openLRSng/openLRSng/openLRSng/RFM.h

#ifndef _RFM_H
#define _RFM_H

// register addresses
#define RFM22B_INTSTAT1     0x03
#define RFM22B_INTSTAT2     0x04
#define RFM22B_INTEN1        0x05
#define RFM22B_INTEN2        0x06
#define RFM22B_OPMODE1     0x07
#define RFM22B_OPMODE2     0x08
#define RFM22B_XTALCAP      0x09
#define RFM22B_MCUCLK       0x0A
#define RFM22B_GPIOCFG0    0x0B
#define RFM22B_GPIOCFG1    0x0C
#define RFM22B_GPIOCFG2    0x0D
#define RFM22B_IOPRTCFG    0x0E

#define RFM22B_IFBW           0x1C
#define RFM22B_AFCLPGR      0x1D
#define RFM22B_AFCTIMG      0x1E
#define RFM22B_RXOSR         0x20
#define RFM22B_NCOFF2       0x21
#define RFM22B_NCOFF1       0x22
#define RFM22B_NCOFF0       0x23
#define RFM22B_CRGAIN1     0x24
#define RFM22B_CRGAIN0     0x25
#define RFM22B_RSSI           0x26
#define RFM22B_AFCLIM       0x2A
#define RFM22B_AFC0          0x2B
#define RFM22B_AFC1          0x2C

#define RFM22B_DACTL    0x30
#define RFM22B_HDRCTL1    0x32
#define RFM22B_HDRCTL2    0x33
#define RFM22B_PREAMLEN  0x34
#define RFM22B_PREATH      0x35
#define RFM22B_SYNC3        0x36
#define RFM22B_SYNC2        0x37
#define RFM22B_SYNC1        0x38
#define RFM22B_SYNC0        0x39

#define RFM22B_TXHDR3      0x3A
#define RFM22B_TXHDR2      0x3B
#define RFM22B_TXHDR1      0x3C
#define RFM22B_TXHDR0      0x3D
#define RFM22B_PKTLEN       0x3E
#define RFM22B_CHKHDR3    0x3F
#define RFM22B_CHKHDR2   0x40
#define RFM22B_CHKHDR1   0x41
#define RFM22B_CHKHDR0   0x42
#define RFM22B_HDREN3     0x43
#define RFM22B_HDREN2     0x44
#define RFM22B_HDREN1     0x45
#define RFM22B_HDREN0     0x46
#define RFM22B_RXPLEN      0x4B

#define RFM22B_TXPOWER   0x6D
#define RFM22B_TXDR1        0x6E
#define RFM22B_TXDR0        0x6F

#define RFM22B_MODCTL1      0x70
#define RFM22B_MODCTL2      0x71
#define RFM22B_FREQDEV      0x72
#define RFM22B_FREQOFF1     0x73
#define RFM22B_FREQOFF2     0x74
#define RFM22B_BANDSEL      0x75
#define RFM22B_CARRFREQ1  0x76
#define RFM22B_CARRFREQ0  0x77
#define RFM22B_FHCH           0x79
#define RFM22B_FHS             0x7A
#define RFM22B_TX_FIFO_CTL1    0x7C
#define RFM22B_TX_FIFO_CTL2    0x7D
#define RFM22B_RX_FIFO_CTL     0x7E
#define RFM22B_FIFO            0x7F

// register fields
#define RFM22B_OPMODE_POWERDOWN    0x00
#define RFM22B_OPMODE_READY    0x01  // enable READY mode
#define RFM22B_OPMODE_TUNE      0x02  // enable TUNE mode
#define RFM22B_OPMODE_RX      0x04  // enable RX mode
#define RFM22B_OPMODE_TX      0x08  // enable TX mode
#define RFM22B_OPMODE_32K      0x10  // enable internal 32k xtal
#define RFM22B_OPMODE_WUT    0x40  // wake up timer
#define RFM22B_OPMODE_LBD     0x80  // low battery detector

#define RFM22B_PACKET_SENT_INTERRUPT               0x04
#define RFM22B_RX_PACKET_RECEIVED_INTERRUPT   0x02

void rfmInit(uint8_t diversity);
void rfmClearInterrupts(void);
void rfmClearIntStatus(void);
void rfmClearFIFO(uint8_t diversity);
void rfmSendPacket(uint8_t* pkt, uint8_t size);

uint16_t rfmGetAFCC(void);
uint8_t rfmGetGPIO1(void);
uint8_t rfmGetRSSI(void);
uint8_t rfmGetPacketLength(void);
void rfmGetPacket(uint8_t *buf, uint8_t size);

void rfmSetTX(void);
void rfmSetRX(void);
void rfmSetCarrierFrequency(uint32_t f);
void rfmSetChannel(uint8_t ch);
void rfmSetDirectOut(uint8_t enable);
void rfmSetHeader(uint8_t iHdr, uint8_t bHdr);
void rfmSetModemRegs(struct rfm22_modem_regs* r);
void rfmSetPower(uint8_t p);
void rfmSetReadyMode(void);
void rfmSetStepSize(uint8_t sp);

void rfmInit(uint8_t diversity)
{
  spiWriteRegister(RFM22B_INTEN2, 0x00);    // disable interrupts
  spiWriteRegister(RFM22B_INTEN1, 0x00);    // disable interrupts
  spiWriteRegister(RFM22B_XTALCAP, 0x7F);   // XTAL cap = 12.5pF
  spiWriteRegister(RFM22B_MCUCLK, 0x05);    // 2MHz clock

  spiWriteRegister(RFM22B_GPIOCFG2, (diversity ? 0x17 : 0xFD) ); // gpio 2 ant. sw, 1 if diversity on else VDD
  spiWriteRegister(RFM22B_PREAMLEN, (diversity ? 0x14 : 0x0A) );    // 40 bit preamble, 80 with diversity
  spiWriteRegister(RFM22B_IOPRTCFG, 0x00);    // gpio 0,1,2 NO OTHER FUNCTION.

  #ifdef SWAP_GPIOS
  spiWriteRegister(RFM22B_GPIOCFG0, 0x15);    // gpio0 RX State
  spiWriteRegister(RFM22B_GPIOCFG1, 0x12);    // gpio1 TX State
  #else
  spiWriteRegister(RFM22B_GPIOCFG0, 0x12);    // gpio0 TX State
  spiWriteRegister(RFM22B_GPIOCFG1, 0x15);    // gpio1 RX State
  #endif

  // Packet settings
  spiWriteRegister(RFM22B_DACTL, 0x8C);    // enable packet handler, msb first, enable crc,
  spiWriteRegister(RFM22B_HDRCTL1, 0x0F);    // no broadcast, check header bytes 3,2,1,0
  spiWriteRegister(RFM22B_HDRCTL2, 0x42);    // 4 byte header, 2 byte sync, variable packet size
  spiWriteRegister(RFM22B_PREATH, 0x2A);    // preamble detect = 5 (20bits), rssioff = 2
  spiWriteRegister(RFM22B_SYNC3, 0x2D);    // sync word 3
  spiWriteRegister(RFM22B_SYNC2, 0xD4);    // sync word 2
  spiWriteRegister(RFM22B_SYNC1, 0x00);    // sync word 1 (not used)
  spiWriteRegister(RFM22B_SYNC0, 0x00);    // sync word 0 (not used)
  spiWriteRegister(RFM22B_HDREN3, 0xFF);    // must set all bits
  spiWriteRegister(RFM22B_HDREN2, 0xFF);    // must set all bits
  spiWriteRegister(RFM22B_HDREN1, 0xFF);    // must set all bits
  spiWriteRegister(RFM22B_HDREN0, 0xFF);    // must set all bits

  spiWriteRegister(RFM22B_FREQOFF1, 0x00);    // no offset
  spiWriteRegister(RFM22B_FREQOFF2, 0x00);    // no offset
  spiWriteRegister(RFM22B_FHCH,        0x00);   // set to hop channel 0
}

void rfmClearFIFO(uint8_t diversity)
{
  //clear FIFO, disable multi-packet, enable diversity if needed
  //requires two write ops, set & clear
  spiWriteRegister(RFM22B_OPMODE2, (diversity ? 0x83 : 0x03) );
  spiWriteRegister(RFM22B_OPMODE2, (diversity ? 0x80 : 0x00) );
}

void rfmClearInterrupts(void)
{
  spiWriteRegister(RFM22B_INTEN1, 0x00);
  spiWriteRegister(RFM22B_INTEN2, 0x00);
}

void rfmClearIntStatus(void)
{
  spiReadRegister(RFM22B_INTSTAT1);
  spiReadRegister(RFM22B_INTSTAT2);
}

void rfmSendPacket(uint8_t* pkt, uint8_t size)
{
  spiWriteRegister(RFM22B_PKTLEN, size);   // total tx size
  for (uint8_t i = 0; i < size; i++) {
    spiWriteRegister(RFM22B_FIFO, pkt[i]);
  }
  spiWriteRegister(RFM22B_INTEN1, RFM22B_PACKET_SENT_INTERRUPT);
}

uint16_t rfmGetAFCC(void)
{
  return (((uint16_t) spiReadRegister(RFM22B_AFC0) << 2) | ((uint16_t) spiReadRegister(RFM22B_AFC1) >> 6));
}

uint8_t rfmGetGPIO1(void)
{
  return spiReadRegister(RFM22B_GPIOCFG1);
}

uint8_t rfmGetRSSI(void)
{
  return spiReadRegister(RFM22B_RSSI);
}

uint8_t rfmGetPacketLength(void)
{
  return spiReadRegister(RFM22B_RXPLEN);
}

void rfmGetPacket(uint8_t *buf, uint8_t size)
{
  // Send the package read command
  spiSendAddress(RFM22B_FIFO);
  for (uint8_t i = 0; i < size; i++) {
    buf[i] = spiReadData();
  }
}

void rfmSetTX(void)
{
  spiWriteRegister(RFM22B_OPMODE1, (RFM22B_OPMODE_TX | RFM22B_OPMODE_READY));
  delayMicroseconds(200); // allow for PLL & PA ramp-up, ~200us
}

void rfmSetRX(void)
{
  spiWriteRegister(RFM22B_INTEN1, RFM22B_RX_PACKET_RECEIVED_INTERRUPT);
  spiWriteRegister(RFM22B_OPMODE1, (RFM22B_OPMODE_RX | RFM22B_OPMODE_READY));
  delayMicroseconds(200);  // allow for PLL ramp-up, ~200us
}

void rfmSetCarrierFrequency(uint32_t f)
{
  uint16_t fb, fc, hbsel;
  if (f < 480000000) {
    hbsel = 0;
    fb = f / 10000000 - 24;
    fc = (f - (fb + 24) * 10000000) * 4 / 625;
  } else {
    hbsel = 1;
    fb = f / 20000000 - 24;
    fc = (f - (fb + 24) * 20000000) * 2 / 625;
  }
  spiWriteRegister(RFM22B_BANDSEL, 0x40 + (hbsel ? 0x20 : 0) + (fb & 0x1f));
  spiWriteRegister(RFM22B_CARRFREQ1, (fc >> 8));
  spiWriteRegister(RFM22B_CARRFREQ0, (fc & 0xff));
  delayMicroseconds(200); // VCO / PLL calibration delay
}

void rfmSetChannel(uint8_t ch)
{
  spiWriteRegister(RFM22B_FHCH, ch);
}

void rfmSetDirectOut(uint8_t enable)
{
 static uint8_t r1 = 0, r2 = 0, r3 = 0;
  if (enable) {
    r1 = spiReadRegister(RFM22B_DACTL);
    r2 = spiReadRegister(RFM22B_MODCTL2);
    r3 = spiReadRegister(RFM22B_FREQDEV);
    // setup for direct output, i.e. beacon tones
    spiWriteRegister(RFM22B_DACTL, 0x00);    //disable packet handling
    spiWriteRegister(RFM22B_MODCTL2, 0x12);    // trclk=[00] no clock, dtmod=[01] direct using SPI, fd8=0 eninv=0 modtyp=[10] FSK
    spiWriteRegister(RFM22B_FREQDEV, 0x02);    // fd (frequency deviation) 2*625Hz == 1.25kHz
  } else {
    // restore previous values
    spiWriteRegister(RFM22B_DACTL, r1);
    spiWriteRegister(RFM22B_MODCTL2, r2);
    spiWriteRegister(RFM22B_FREQDEV, r3); 
  }
}

void rfmSetHeader(uint8_t iHdr, uint8_t bHdr)
{
  spiWriteRegister(RFM22B_TXHDR3+iHdr, bHdr);
  spiWriteRegister(RFM22B_CHKHDR3+iHdr, bHdr);
}

void rfmSetModemRegs(struct rfm22_modem_regs* r)
{
  spiWriteRegister(RFM22B_IFBW,        r->r_1c);
  spiWriteRegister(RFM22B_AFCLPGR,   r->r_1d);
  spiWriteRegister(RFM22B_AFCTIMG,   r->r_1e);
  spiWriteRegister(RFM22B_RXOSR,      r->r_20);
  spiWriteRegister(RFM22B_NCOFF2,     r->r_21);
  spiWriteRegister(RFM22B_NCOFF1,     r->r_22);
  spiWriteRegister(RFM22B_NCOFF0,     r->r_23);
  spiWriteRegister(RFM22B_CRGAIN1,   r->r_24);
  spiWriteRegister(RFM22B_CRGAIN0,   r->r_25);
  spiWriteRegister(RFM22B_AFCLIM,     r->r_2a);
  spiWriteRegister(RFM22B_TXDR1,      r->r_6e);
  spiWriteRegister(RFM22B_TXDR0,      r->r_6f);
  spiWriteRegister(RFM22B_MODCTL1,  r->r_70);
  spiWriteRegister(RFM22B_MODCTL2,  r->r_71);
  spiWriteRegister(RFM22B_FREQDEV,  r->r_72);
}

void rfmSetPower(uint8_t power)
{
  spiWriteRegister(RFM22B_TXPOWER, power);
  delayMicroseconds(25); // PA ramp up/down time
}

void rfmSetReadyMode(void)
{
  spiWriteRegister(RFM22B_OPMODE1, RFM22B_OPMODE_READY);
}

void rfmSetStepSize(uint8_t sp)
{
  spiWriteRegister(RFM22B_FHS, sp);
}

#endif
